R2AKT/eMMU/eMMU.kicad_sch

## KiCad design eMMU.kicad_sch (2026-06-29)

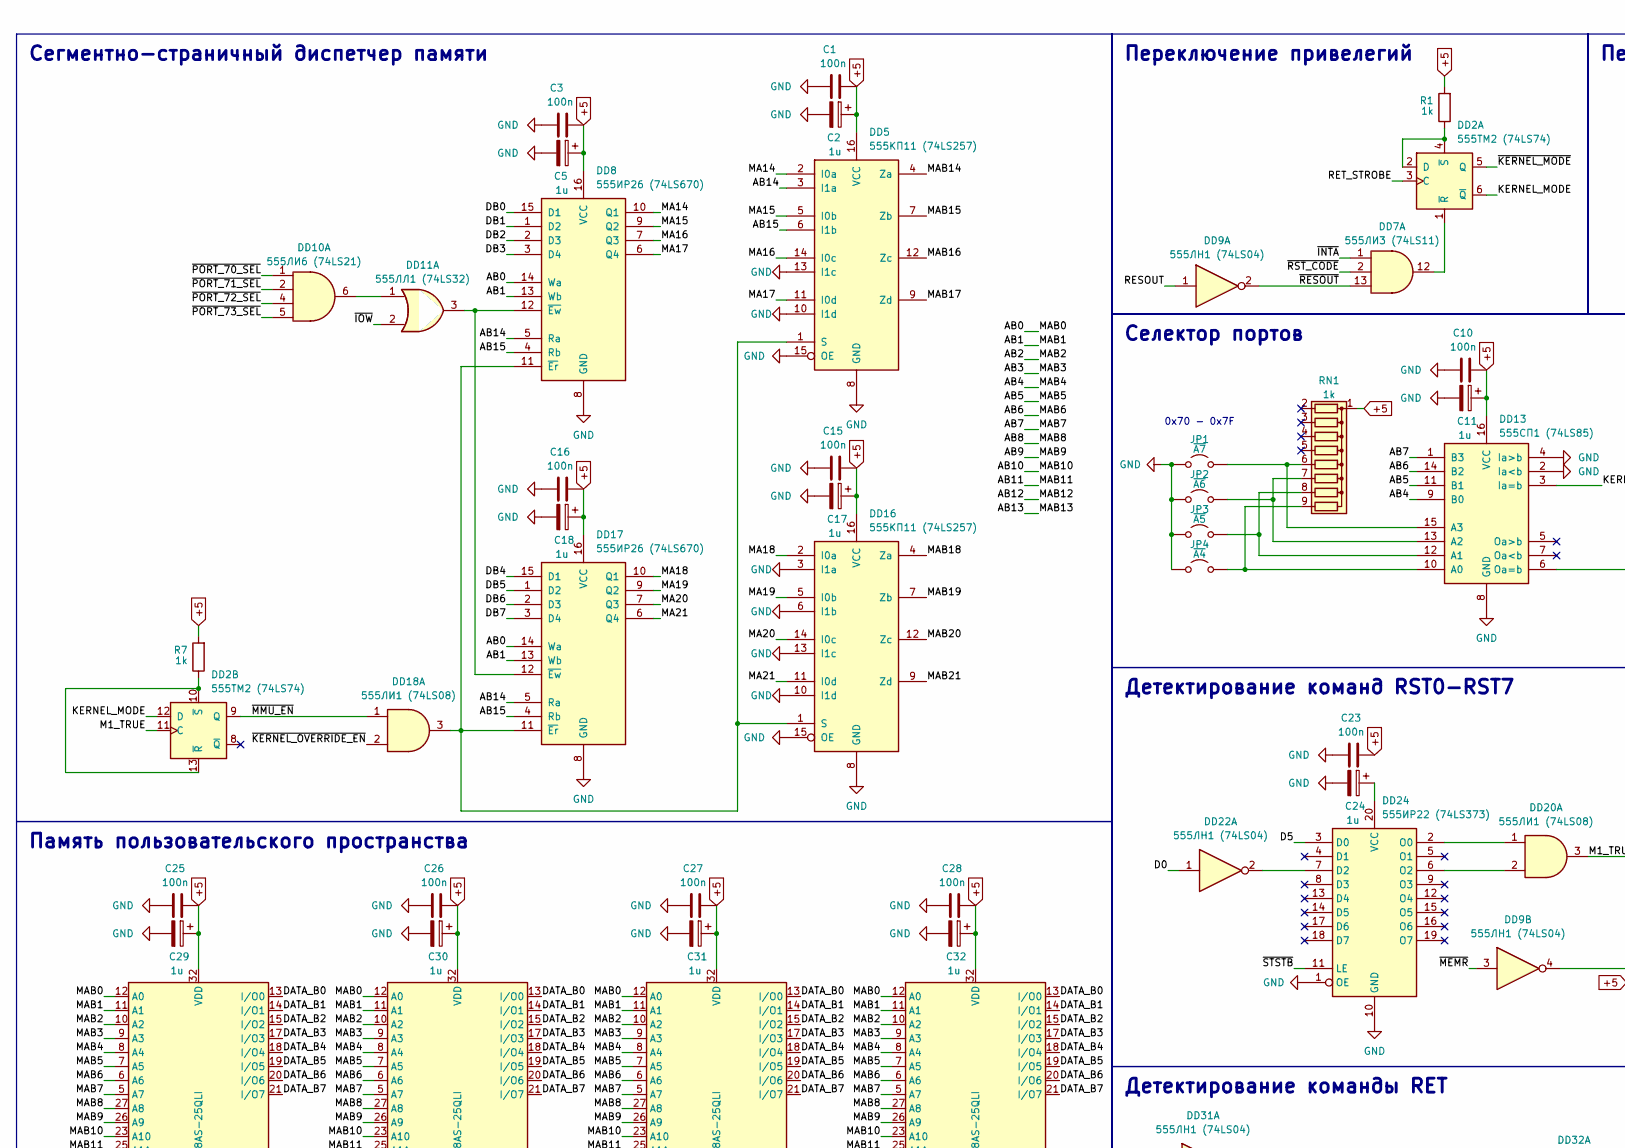
[picture p2: schematic eMMU.kicad_sch, part in row 1, column 1]

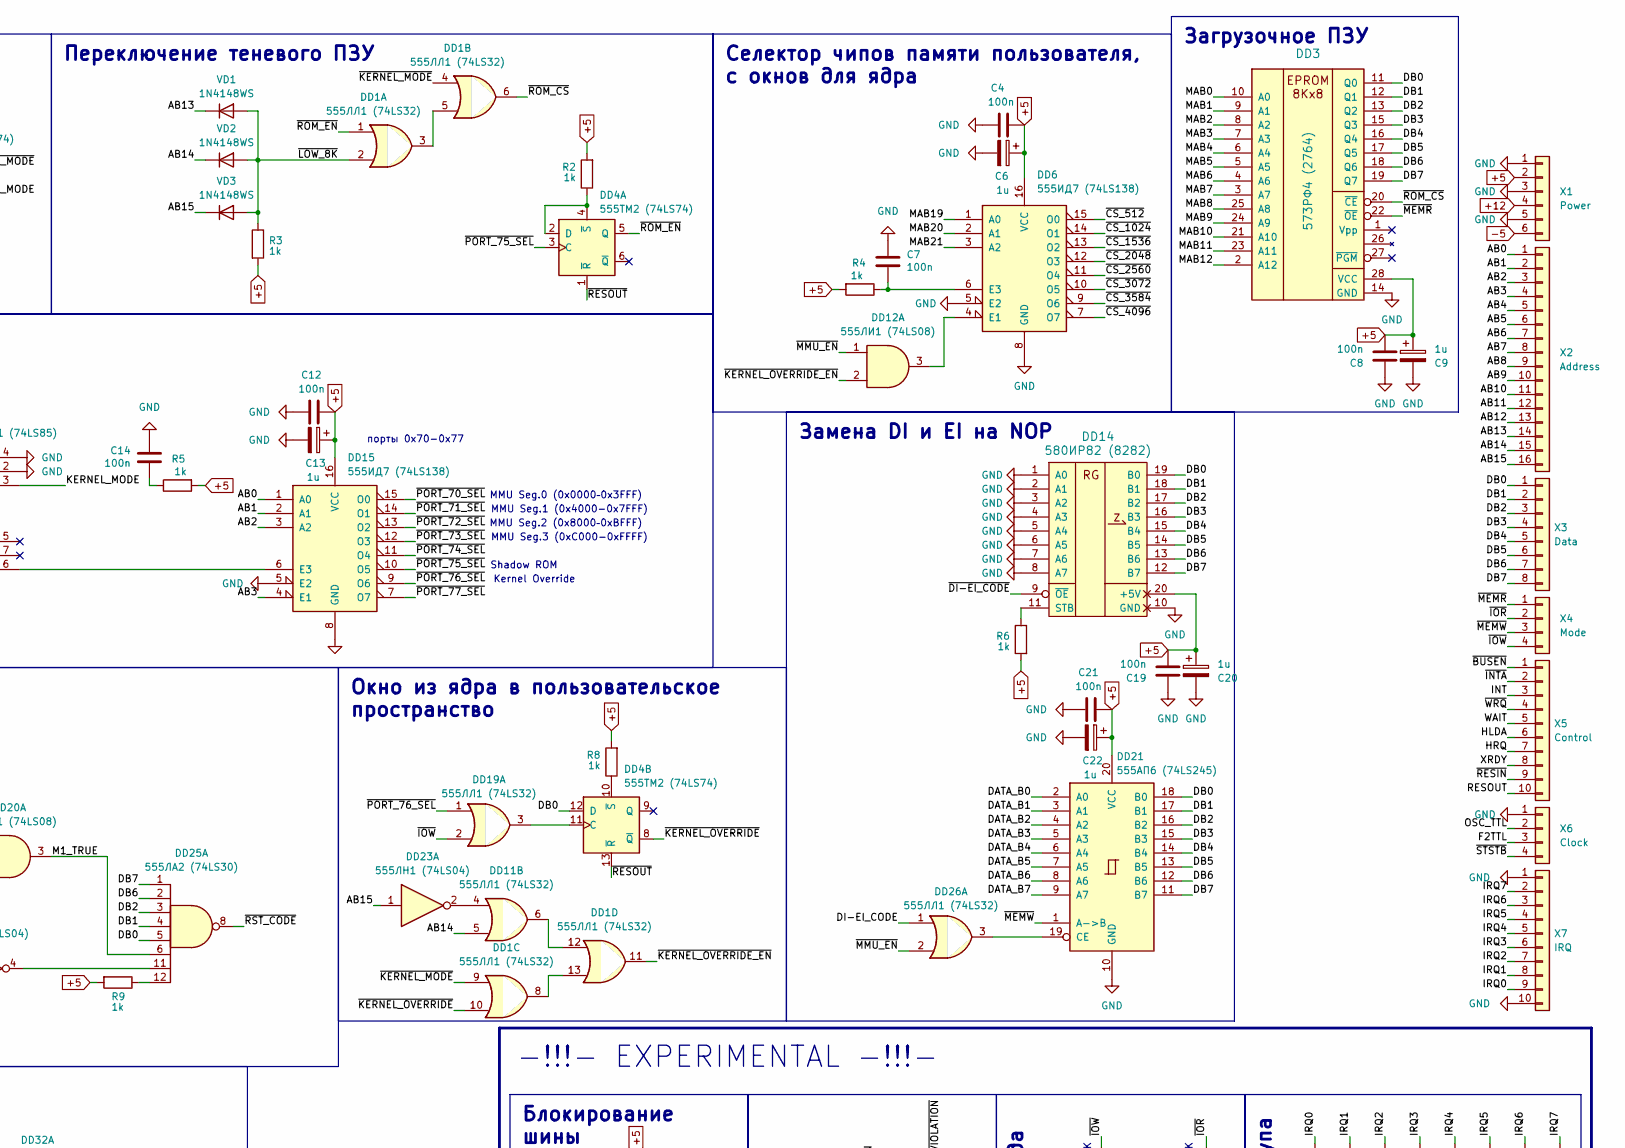
[picture p3: schematic eMMU.kicad_sch, part in row 1, column 2]

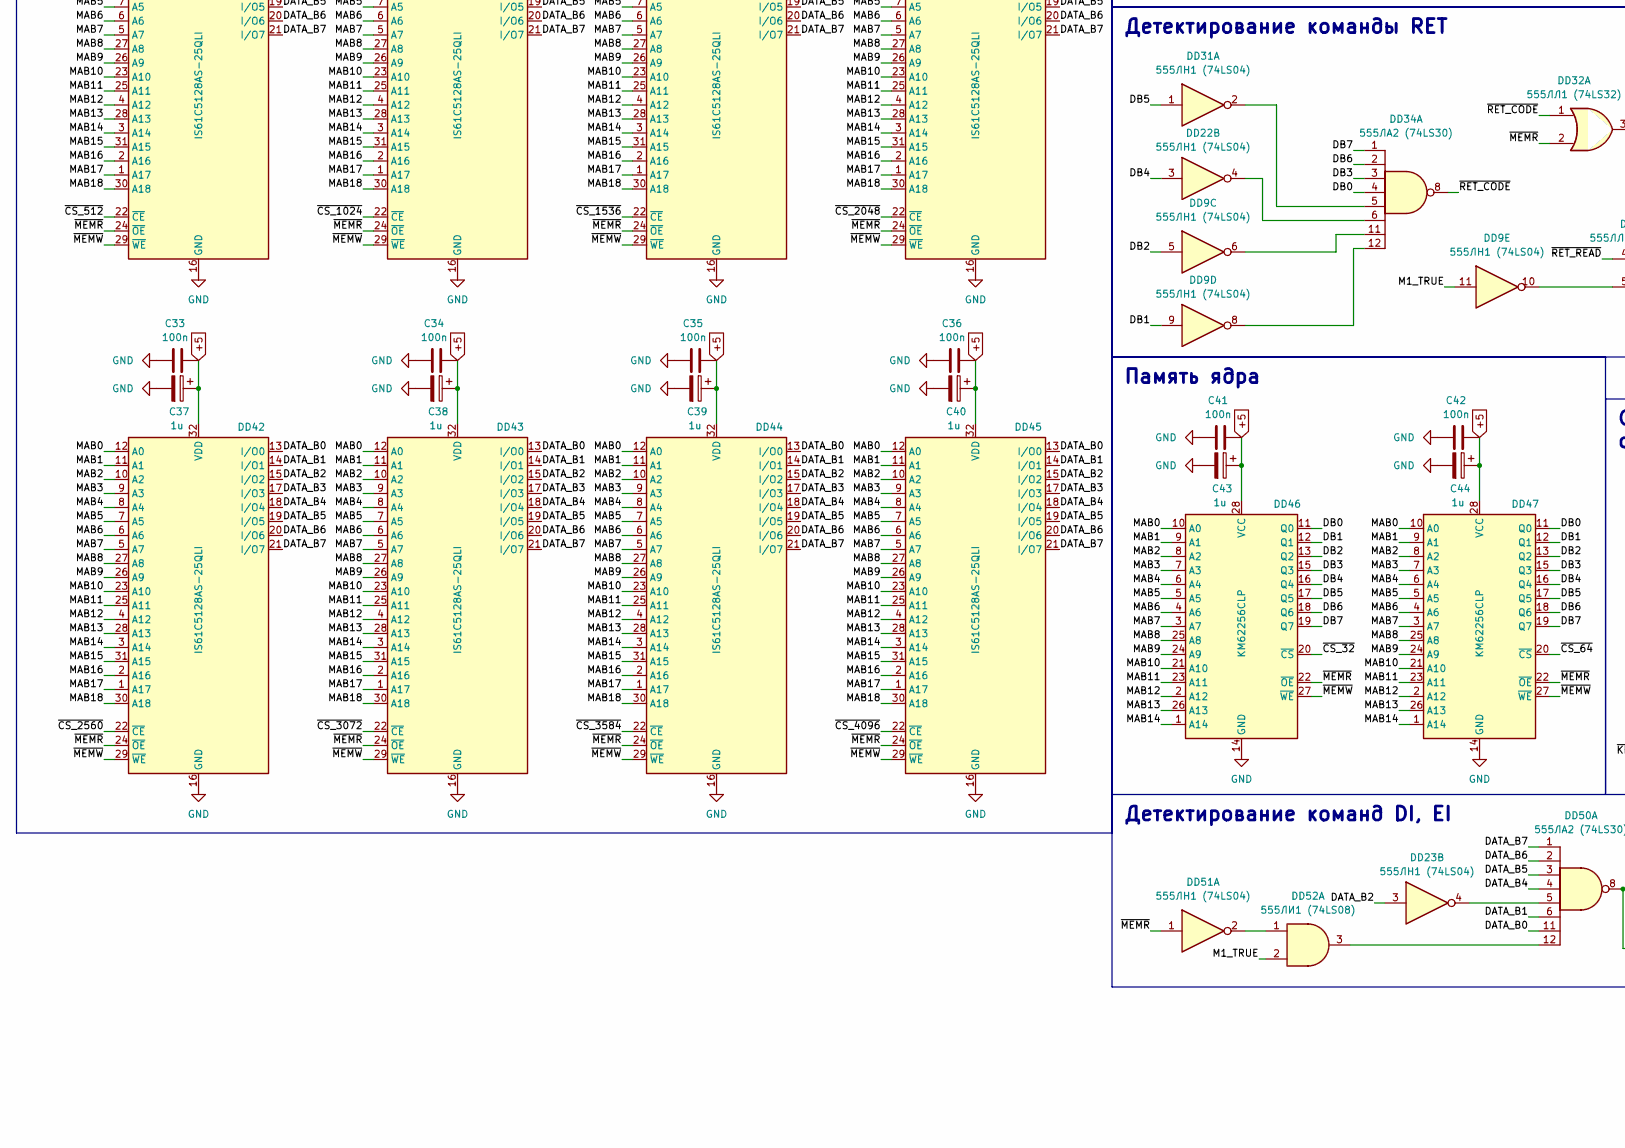
[picture p4: schematic eMMU.kicad_sch, part in row 2, column 1]

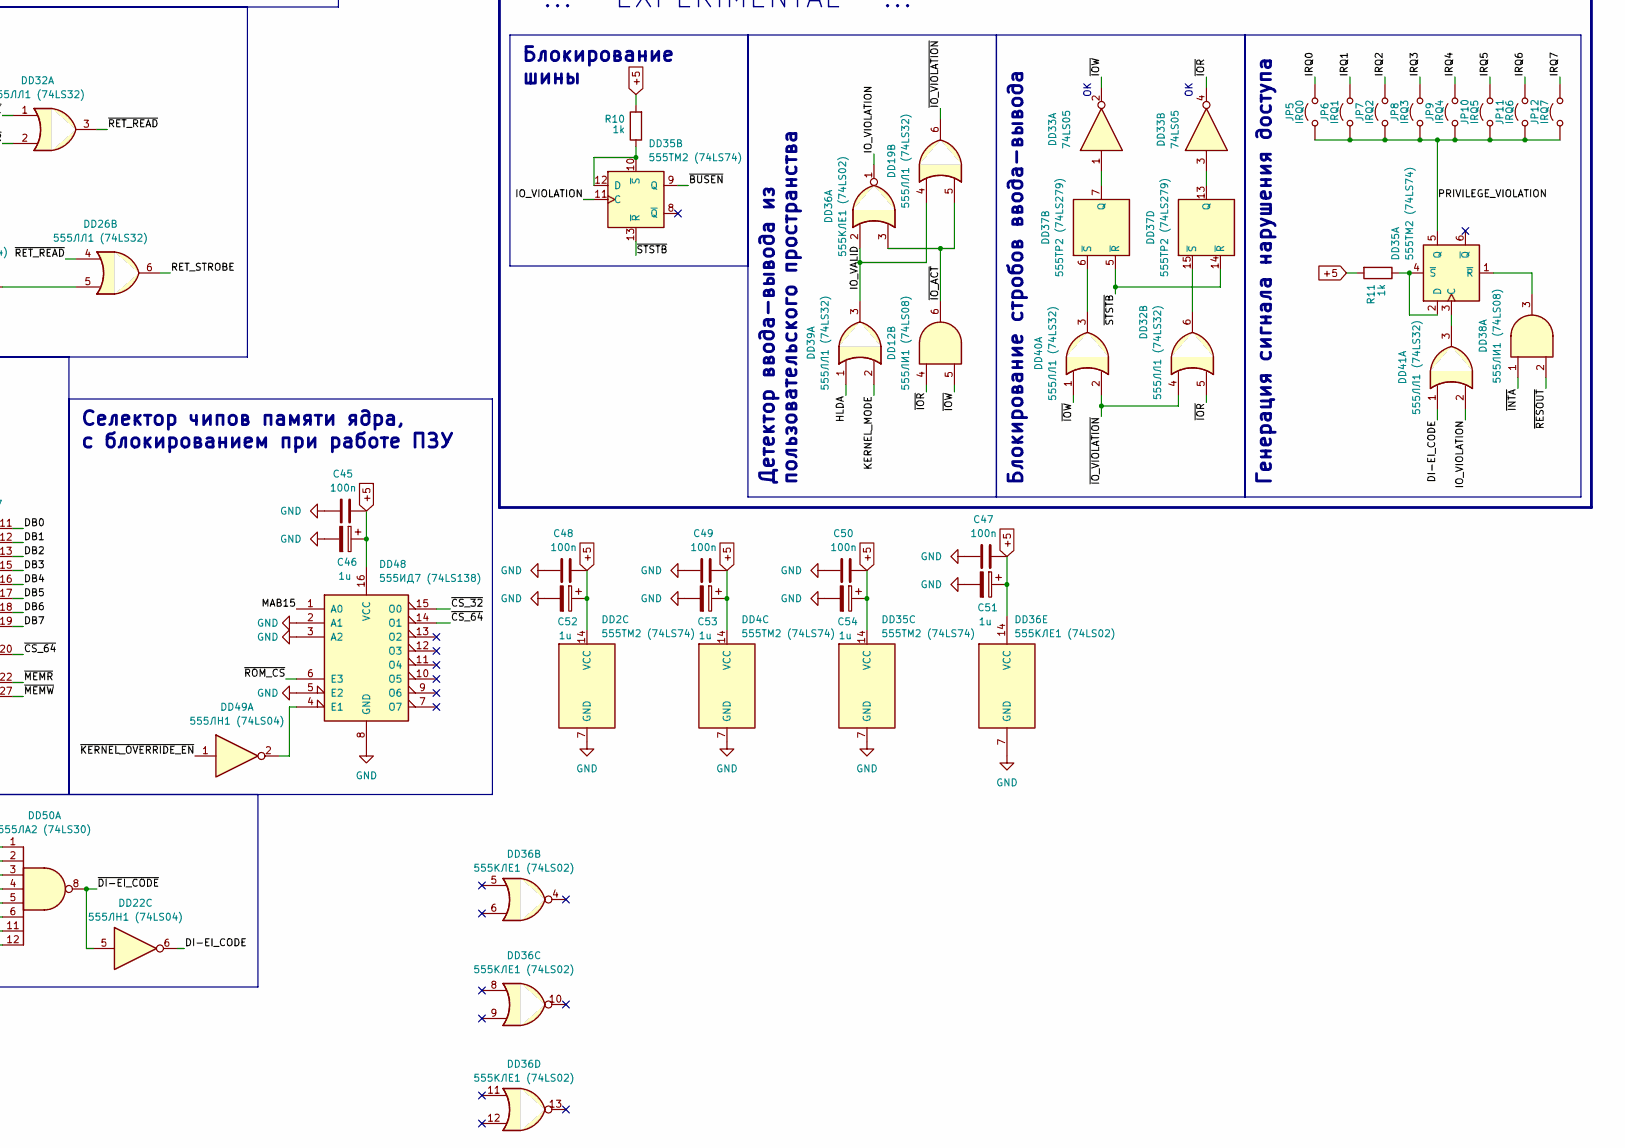
[picture p5: schematic eMMU.kicad_sch, part in row 2, column 2]

Parts:
C1, C3, C4, C7, C8, C10, C12, C14, C15, C16, C19, C21, C23, C25, C26, C27, C28, C33, C34, C35, C36, C41, C42, C45, C47, C48, C49, C50: 100n; C_0805_2012Metric_Pad1.18x1.45mm_HandSolder
C2, C5, C6, C9, C11, C13, C17, C18, C20, C22, C24, C29, C30, C31, C32, C37, C38, C39, C40, C43, C44, C46, C51, C52, C53, C54: 1u; CP_EIA-3216-18_Kemet-A_Pad1.58x1.35mm_HandSolder
DD1, DD11, DD19, DD26, DD32, DD39, DD40, DD41: 555ЛЛ1 (74LS32); SOIC-14_3.9x8.7mm_P1.27mm
DD2, DD4, DD35: 555ТМ2 (74LS74); SOIC-14_3.9x8.7mm_P1.27mm
DD3: 573РФ4 (2764); DIP-28_W15.24mm_Socket_LongPads
DD5, DD16: 555КП11 (74LS257); SOIC-16_4.55x10.3mm_P1.27mm
DD6, DD15, DD48: 555ИД7 (74LS138); SOIC-16_4.55x10.3mm_P1.27mm
DD7: 555ЛИ3 (74LS11); SOIC-14_3.9x8.7mm_P1.27mm
DD8, DD17: 555ИР26 (74LS670); SOIC-16_4.55x10.3mm_P1.27mm
DD9, DD22, DD23, DD31, DD49, DD51: 555ЛН1 (74LS04); SOIC-14_3.9x8.7mm_P1.27mm
DD10: 555ЛИ6 (74LS21); SOIC-14_3.9x8.7mm_P1.27mm
DD12, DD18, DD20, DD38, DD52: 555ЛИ1 (74LS08); SOIC-14_3.9x8.7mm_P1.27mm
DD13: 555СП1 (74LS85); SOIC-16_4.55x10.3mm_P1.27mm
DD14: 580ИР82 (8282); DIP-20_W7.62mm_LongPads
DD21: 555АП6 (74LS245); DIP-20_W7.62mm_Socket_LongPads
DD24: 555ИР22 (74LS373); SOIC-20W_7.5x12.8mm_P1.27mm
DD25, DD34, DD50: 555ЛА2 (74LS30); SOIC-14_3.9x8.7mm_P1.27mm
DD27, DD28, DD29, DD30, DD42, DD43, DD44, DD45: IS61C5128AS-25QLI; SOP-32_11.305x20.495mm_P1.27mm
DD33: 74LS05; SOIC-14_3.9x8.7mm_P1.27mm
DD36: 555KЛЕ1 (74LS02); SOIC-14_3.9x8.7mm_P1.27mm
DD37: 555ТР2 (74LS279); SOIC-16_4.55x10.3mm_P1.27mm
DD46, DD47: KM62256CLP; SOP-28_8.4x18.16mm_P1.27mm
JP1: ~{A7}; SolderJumper-2_P1.3mm_Open_RoundedPad1.0x1.5mm
JP2: ~{A6}; SolderJumper-2_P1.3mm_Open_RoundedPad1.0x1.5mm
JP3: ~{A5}; SolderJumper-2_P1.3mm_Open_RoundedPad1.0x1.5mm
JP4: ~{A4}; SolderJumper-2_P1.3mm_Open_RoundedPad1.0x1.5mm
JP5: IRQ0; SolderJumper-2_P1.3mm_Open_RoundedPad1.0x1.5mm
JP6: IRQ1; SolderJumper-2_P1.3mm_Open_RoundedPad1.0x1.5mm
JP7: IRQ2; SolderJumper-2_P1.3mm_Open_RoundedPad1.0x1.5mm
JP8: IRQ3; SolderJumper-2_P1.3mm_Open_RoundedPad1.0x1.5mm
JP9: IRQ4; SolderJumper-2_P1.3mm_Open_RoundedPad1.0x1.5mm
JP10: IRQ5; SolderJumper-2_P1.3mm_Open_RoundedPad1.0x1.5mm
JP11: IRQ6; SolderJumper-2_P1.3mm_Open_RoundedPad1.0x1.5mm
JP12: IRQ7; SolderJumper-2_P1.3mm_Open_RoundedPad1.0x1.5mm
R1, R2, R3, R4, R5, R6, R7, R8, R9, R10, R11: 1k; R_0805_2012Metric_Pad1.20x1.40mm_HandSolder
RN1: 1k; R_Array_SIP9
VD1, VD2, VD3: 1N4148WS; D_SOD-323_HandSoldering
X1: Power; PinHeader_1x06_P2.54mm_Vertical
X2: Address; PinHeader_1x16_P2.54mm_Vertical
X3: Data; PinHeader_1x08_P2.54mm_Vertical
X4: Mode; PinHeader_1x04_P2.54mm_Vertical
X5: Control; PinHeader_1x10_P2.54mm_Vertical
X6: Clock; PinHeader_1x04_P2.54mm_Vertical
X7: IRQ; PinHeader_1x10_P2.54mm_Vertical

Connections:
+5: C1.1, C2.1, C3.1, C4.1, C5.1, C6.1, C8.1, C9.1, C10.1, C11.1, C12.1, C13.1, C15.1, C16.1, C17.1, C18.1, C19.1, C20.1, C21.1, C22.1, C23.1, C25.1, C26.1, C27.1, C28.1, C29.1, C30.1, C31.1, C32.1, C33.1, C34.1, C35.1, C36.1, C37.1, C38.1, C39.1, C40.1, C41.1, C42.1, C43.1, C44.1, C45.1, C46.1, C47.1, C48.1, C49.1, C50.1, C51.1, C52.1, C53.1, C54.1, DD2.14 (VCC), DD3.28 (VCC), DD4.14 (VCC), DD5.16 (VCC), DD6.16 (VCC), DD8.16 (VCC), DD13.16 (VCC), DD14.20 (+5V), DD15.16 (VCC), DD16.16 (VCC), DD17.16 (VCC), DD21.20 (VCC), DD27.32 (VDD), DD28.32 (VDD), DD29.32 (VDD), DD30.32 (VDD), DD35.14 (VCC), DD36.14 (VCC), DD42.32 (VDD), DD43.32 (VDD), DD44.32 (VDD), DD45.32 (VDD), DD46.28 (VCC), DD47.28 (VCC), DD48.16 (VCC), R1.2, R2.2, R3.2, R4.2, R5.2, R6.2, R7.2, R8.2, R9.2, R10.2, R11.2, RN1.1 (common), X1.2
+12: X1.4
-5: X1.6
AB0: DD3.10 (A0), DD8.14 (Wa), DD15.1 (A0), DD17.14 (Wa), DD27.12 (A0), DD28.12 (A0), DD29.12 (A0), DD30.12 (A0), DD42.12 (A0), DD43.12 (A0), DD44.12 (A0), DD45.12 (A0), DD46.10 (A0), DD47.10 (A0), X2.1
AB1: DD3.9 (A1), DD8.13 (Wb), DD15.2 (A1), DD17.13 (Wb), DD27.11 (A1), DD28.11 (A1), DD29.11 (A1), DD30.11 (A1), DD42.11 (A1), DD43.11 (A1), DD44.11 (A1), DD45.11 (A1), DD46.9 (A1), DD47.9 (A1), X2.2
AB2: DD3.8 (A2), DD15.3 (A2), DD27.10 (A2), DD28.10 (A2), DD29.10 (A2), DD30.10 (A2), DD42.10 (A2), DD43.10 (A2), DD44.10 (A2), DD45.10 (A2), DD46.8 (A2), DD47.8 (A2), X2.3
AB3: DD3.7 (A3), DD15.4 (E1), DD27.9 (A3), DD28.9 (A3), DD29.9 (A3), DD30.9 (A3), DD42.9 (A3), DD43.9 (A3), DD44.9 (A3), DD45.9 (A3), DD46.7 (A3), DD47.7 (A3), X2.4
AB4: DD3.6 (A4), DD13.9 (B0), DD27.8 (A4), DD28.8 (A4), DD29.8 (A4), DD30.8 (A4), DD42.8 (A4), DD43.8 (A4), DD44.8 (A4), DD45.8 (A4), DD46.6 (A4), DD47.6 (A4), X2.5
AB5: DD3.5 (A5), DD13.11 (B1), DD27.7 (A5), DD28.7 (A5), DD29.7 (A5), DD30.7 (A5), DD42.7 (A5), DD43.7 (A5), DD44.7 (A5), DD45.7 (A5), DD46.5 (A5), DD47.5 (A5), X2.6
AB6: DD3.4 (A6), DD13.14 (B2), DD27.6 (A6), DD28.6 (A6), DD29.6 (A6), DD30.6 (A6), DD42.6 (A6), DD43.6 (A6), DD44.6 (A6), DD45.6 (A6), DD46.4 (A6), DD47.4 (A6), X2.7
AB7: DD3.3 (A7), DD13.1 (B3), DD27.5 (A7), DD28.5 (A7), DD29.5 (A7), DD30.5 (A7), DD42.5 (A7), DD43.5 (A7), DD44.5 (A7), DD45.5 (A7), DD46.3 (A7), DD47.3 (A7), X2.8
AB8: DD3.25 (A8), DD27.27 (A8), DD28.27 (A8), DD29.27 (A8), DD30.27 (A8), DD42.27 (A8), DD43.27 (A8), DD44.27 (A8), DD45.27 (A8), DD46.25 (A8), DD47.25 (A8), X2.9
AB9: DD3.24 (A9), DD27.26 (A9), DD28.26 (A9), DD29.26 (A9), DD30.26 (A9), DD42.26 (A9), DD43.26 (A9), DD44.26 (A9), DD45.26 (A9), DD46.24 (A9), DD47.24 (A9), X2.10
AB10: DD3.21 (A10), DD27.23 (A10), DD28.23 (A10), DD29.23 (A10), DD30.23 (A10), DD42.23 (A10), DD43.23 (A10), DD44.23 (A10), DD45.23 (A10), DD46.21 (A10), DD47.21 (A10), X2.11
AB11: DD3.23 (A11), DD27.25 (A11), DD28.25 (A11), DD29.25 (A11), DD30.25 (A11), DD42.25 (A11), DD43.25 (A11), DD44.25 (A11), DD45.25 (A11), DD46.23 (A11), DD47.23 (A11), X2.12
AB12: DD3.2 (A12), DD27.4 (A12), DD28.4 (A12), DD29.4 (A12), DD30.4 (A12), DD42.4 (A12), DD43.4 (A12), DD44.4 (A12), DD45.4 (A12), DD46.2 (A12), DD47.2 (A12), X2.13
AB13: DD27.28 (A13), DD28.28 (A13), DD29.28 (A13), DD30.28 (A13), DD42.28 (A13), DD43.28 (A13), DD44.28 (A13), DD45.28 (A13), DD46.26 (A13), DD47.26 (A13), VD1.1 (K), X2.14
AB14: DD5.3 (I1a), DD8.5 (Ra), DD11.5, DD17.5 (Ra), VD2.1 (K), X2.15
AB15: DD5.6 (I1b), DD8.4 (Rb), DD17.4 (Rb), DD23.1, VD3.1 (K), X2.16
D0: DD22.1
D5: DD24.3 (D0)
DATA_B0: DD21.2 (A0), DD27.13 (I/O0), DD28.13 (I/O0), DD29.13 (I/O0), DD30.13 (I/O0), DD42.13 (I/O0), DD43.13 (I/O0), DD44.13 (I/O0), DD45.13 (I/O0), DD50.11
DATA_B1: DD21.3 (A1), DD27.14 (I/O1), DD28.14 (I/O1), DD29.14 (I/O1), DD30.14 (I/O1), DD42.14 (I/O1), DD43.14 (I/O1), DD44.14 (I/O1), DD45.14 (I/O1), DD50.6
DATA_B2: DD21.4 (A2), DD23.3, DD27.15 (I/O2), DD28.15 (I/O2), DD29.15 (I/O2), DD30.15 (I/O2), DD42.15 (I/O2), DD43.15 (I/O2), DD44.15 (I/O2), DD45.15 (I/O2)
DATA_B3: DD21.5 (A3), DD27.17 (I/O3), DD28.17 (I/O3), DD29.17 (I/O3), DD30.17 (I/O3), DD42.17 (I/O3), DD43.17 (I/O3), DD44.17 (I/O3), DD45.17 (I/O3)
DATA_B4: DD21.6 (A4), DD27.18 (I/O4), DD28.18 (I/O4), DD29.18 (I/O4), DD30.18 (I/O4), DD42.18 (I/O4), DD43.18 (I/O4), DD44.18 (I/O4), DD45.18 (I/O4), DD50.4
DATA_B5: DD21.7 (A5), DD27.19 (I/O5), DD28.19 (I/O5), DD29.19 (I/O5), DD30.19 (I/O5), DD42.19 (I/O5), DD43.19 (I/O5), DD44.19 (I/O5), DD45.19 (I/O5), DD50.3
DATA_B6: DD21.8 (A6), DD27.20 (I/O6), DD28.20 (I/O6), DD29.20 (I/O6), DD30.20 (I/O6), DD42.20 (I/O6), DD43.20 (I/O6), DD44.20 (I/O6), DD45.20 (I/O6), DD50.2
DATA_B7: DD21.9 (A7), DD27.21 (I/O7), DD28.21 (I/O7), DD29.21 (I/O7), DD30.21 (I/O7), DD42.21 (I/O7), DD43.21 (I/O7), DD44.21 (I/O7), DD45.21 (I/O7), DD50.1
DB0: DD3.11 (Q0), DD4.12 (D), DD8.15 (D1), DD14.19 (B0), DD21.18 (B0), DD25.5, DD34.4, DD46.11 (Q0), DD47.11 (Q0), X3.1
DB1: DD3.12 (Q1), DD8.1 (D2), DD9.9, DD14.18 (B1), DD21.17 (B1), DD25.4, DD46.12 (Q1), DD47.12 (Q1), X3.2
DB2: DD3.13 (Q2), DD8.2 (D3), DD9.5, DD14.17 (B2), DD21.16 (B2), DD25.3, DD46.13 (Q2), DD47.13 (Q2), X3.3
DB3: DD3.15 (Q3), DD8.3 (D4), DD14.16 (B3), DD21.15 (B3), DD34.3, DD46.15 (Q3), DD47.15 (Q3), X3.4
DB4: DD3.16 (Q4), DD14.15 (B4), DD17.15 (D1), DD21.14 (B4), DD22.3, DD46.16 (Q4), DD47.16 (Q4), X3.5
DB5: DD3.17 (Q5), DD14.14 (B5), DD17.1 (D2), DD21.13 (B5), DD31.1, DD46.17 (Q5), DD47.17 (Q5), X3.6
DB6: DD3.18 (Q6), DD14.13 (B6), DD17.2 (D3), DD21.12 (B6), DD25.2, DD34.2, DD46.18 (Q6), DD47.18 (Q6), X3.7
DB7: DD3.19 (Q7), DD14.12 (B7), DD17.3 (D4), DD21.11 (B7), DD25.1, DD34.1, DD46.19 (Q7), DD47.19 (Q7), X3.8
DI-EI_CODE: DD22.6, DD26.1, DD41.1
F2TTL: X6.3
GND: C1.2, C2.2, C3.2, C4.2, C5.2, C6.2, C7.1, C8.2, C9.2, C10.2, C11.2, C12.2, C13.2, C14.1, C15.2, C16.2, C17.2, C18.2, C19.2, C20.2, C21.2, C22.2, C23.2, C24.2, C25.2, C26.2, C27.2, C28.2, C29.2, C30.2, C31.2, C32.2, C33.2, C34.2, C35.2, C36.2, C37.2, C38.2, C39.2, C40.2, C41.2, C42.2, C43.2, C44.2, C45.2, C46.2, C47.2, C48.2, C49.2, C50.2, C51.2, C52.2, C53.2, C54.2, DD2.7 (GND), DD3.14 (GND), DD4.7 (GND), DD5.8 (GND), DD5.10 (I1d), DD5.13 (I1c), DD5.15 (OE), DD6.5 (E2), DD6.8 (GND), DD8.8 (GND), DD13.2 (Ia<b), DD13.4 (Ia>b), DD13.8 (GND), DD14.1 (A0), DD14.2 (A1), DD14.3 (A2), DD14.4 (A3), DD14.5 (A4), DD14.6 (A5), DD14.7 (A6), DD14.8 (A7), DD14.10 (GND), DD15.5 (E2), DD15.8 (GND), DD16.3 (I1a), DD16.6 (I1b), DD16.8 (GND), DD16.10 (I1d), DD16.13 (I1c), DD16.15 (OE), DD17.8 (GND), DD21.10 (GND), DD24.1 (OE), DD24.10 (GND), DD27.16 (GND), DD28.16 (GND), DD29.16 (GND), DD30.16 (GND), DD35.7 (GND), DD36.7 (GND), DD42.16 (GND), DD43.16 (GND), DD44.16 (GND), DD45.16 (GND), DD46.14 (GND), DD47.14 (GND), DD48.2 (A1), DD48.3 (A2), DD48.5 (E2), DD48.8 (GND), JP1.1 (A), JP2.1 (A), JP3.1 (A), JP4.1 (A), X1.1, X1.3, X1.5, X6.1, X7.1, X7.10
HLDA: DD39.1, X5.6
HRQ: X5.7
INT: X5.3
IO_VALID: DD19.4, DD36.2, DD39.3
IO_VIOLATION: DD35.11 (C), DD36.1, DD41.2
IRQ0: JP5.2 (B), X7.9
IRQ1: JP6.2 (B), X7.8
IRQ2: JP7.2 (B), X7.7
IRQ3: JP8.2 (B), X7.6
IRQ4: JP9.2 (B), X7.5
IRQ5: JP10.2 (B), X7.4
IRQ6: JP11.2 (B), X7.3
IRQ7: JP12.2 (B), X7.2
KERNEL_MODE: DD2.6 (~Q), DD2.12 (D), DD13.3 (Ia=b), DD39.2
M1_TRUE: DD2.11 (C), DD9.11, DD20.3, DD25.6, DD52.2
MA14: DD5.2 (I0a), DD8.10 (Q1)
MA15: DD5.5 (I0b), DD8.9 (Q2)
MA16: DD5.14 (I0c), DD8.7 (Q3)
MA17: DD5.11 (I0d), DD8.6 (Q4)
MA18: DD16.2 (I0a), DD17.10 (Q1)
MA19: DD16.5 (I0b), DD17.9 (Q2)
MA20: DD16.14 (I0c), DD17.7 (Q3)
MA21: DD16.11 (I0d), DD17.6 (Q4)
MAB14: DD5.4 (Za), DD27.3 (A14), DD28.3 (A14), DD29.3 (A14), DD30.3 (A14), DD42.3 (A14), DD43.3 (A14), DD44.3 (A14), DD45.3 (A14), DD46.1 (A14), DD47.1 (A14)
MAB15: DD5.7 (Zb), DD27.31 (A15), DD28.31 (A15), DD29.31 (A15), DD30.31 (A15), DD42.31 (A15), DD43.31 (A15), DD44.31 (A15), DD45.31 (A15), DD48.1 (A0)
MAB16: DD5.12 (Zc), DD27.2 (A16), DD28.2 (A16), DD29.2 (A16), DD30.2 (A16), DD42.2 (A16), DD43.2 (A16), DD44.2 (A16), DD45.2 (A16)
MAB17: DD5.9 (Zd), DD27.1 (A17), DD28.1 (A17), DD29.1 (A17), DD30.1 (A17), DD42.1 (A17), DD43.1 (A17), DD44.1 (A17), DD45.1 (A17)
MAB18: DD16.4 (Za), DD27.30 (A18), DD28.30 (A18), DD29.30 (A18), DD30.30 (A18), DD42.30 (A18), DD43.30 (A18), DD44.30 (A18), DD45.30 (A18)
MAB19: DD6.1 (A0), DD16.7 (Zb)
MAB20: DD6.2 (A1), DD16.12 (Zc)
MAB21: DD6.3 (A2), DD16.9 (Zd)
unnamed: C7.2, DD6.6 (E3), R4.1
unnamed: C14.2, R5.1
unnamed: C24.1, DD24.20 (VCC)
unnamed: DD1.3, DD1.5
unnamed: DD1.12, DD11.6
unnamed: DD1.8, DD1.13
unnamed: DD2.1 (~R), DD7.12
unnamed: DD2.2 (D), DD2.4 (~S), R1.1
unnamed: DD2.10 (~S), DD2.13 (~R), R7.1
unnamed: DD4.2 (D), DD4.4 (~S), R2.1
unnamed: DD4.10 (~S), R8.1
unnamed: DD10.6, DD11.1
unnamed: DD8.12 (~Ew), DD11.3, DD17.12 (~Ew)
unnamed: DD11.4, DD23.2
unnamed: DD6.4 (E1), DD12.3
unnamed: DD13.6 (Oa=b), DD15.6 (E3)
unnamed: DD13.10 (A0), JP4.2 (B), RN1.9 (R8)
unnamed: DD13.12 (A1), JP3.2 (B), RN1.8 (R7)
unnamed: DD13.13 (A2), JP2.2 (B), RN1.7 (R6)
unnamed: DD13.15 (A3), JP1.2 (B), RN1.6 (R5)
unnamed: DD14.11 (STB), R6.1
unnamed: DD5.1 (S), DD8.11 (~Er), DD16.1 (S), DD17.11 (~Er), DD18.3
unnamed: DD4.11 (C), DD19.3
unnamed: DD20.1, DD24.2 (O0)
unnamed: DD20.2, DD24.6 (O2)
unnamed: DD21.19 (CE), DD26.3
unnamed: DD22.2, DD24.7 (D2)
unnamed: DD22.4, DD34.6
unnamed: DD23.4, DD50.5
unnamed: DD9.4, DD25.11
unnamed: DD25.12, R9.1
unnamed: DD9.10, DD26.5
unnamed: DD31.2, DD34.5
unnamed: DD32.6, DD37.15 (~S)
unnamed: DD33.1, DD37.7 (Q)
unnamed: DD33.3, DD37.13 (Q)
unnamed: DD9.6, DD34.11
unnamed: DD9.8, DD34.12
unnamed: DD35.1 (~R), DD38.3
unnamed: DD35.2 (D), DD35.4 (~S), R11.1
unnamed: DD35.3 (C), DD41.3
unnamed: DD35.10 (~S), DD35.12 (D), R10.1
unnamed: DD37.6 (~S), DD40.3
unnamed: DD48.4 (E1), DD49.2
unnamed: DD50.12, DD52.3
unnamed: DD51.2, DD52.1
OSC_TTL: X6.2
PRIVILEGE_VIOLATION: DD35.5 (Q), JP5.1 (A), JP6.1 (A), JP7.1 (A), JP8.1 (A), JP9.1 (A), JP10.1 (A), JP11.1 (A), JP12.1 (A)
RESOUT: DD9.1, X5.10
RET_STROBE: DD2.3 (C), DD26.6
WAIT: X5.5
XRDY: X5.8
~BUSEN: DD35.9 (Q), X5.1
~CS_32: DD46.20 (~CS), DD48.15 (O0)
~CS_64: DD47.20 (~CS), DD48.14 (O1)
~CS_512: DD6.15 (O0), DD27.22 (~CE)
~CS_1024: DD6.14 (O1), DD28.22 (~CE)
~CS_1536: DD6.13 (O2), DD29.22 (~CE)
~CS_2048: DD6.12 (O3), DD30.22 (~CE)
~CS_2560: DD6.11 (O4), DD42.22 (~CE)
~CS_3072: DD6.10 (O5), DD43.22 (~CE)
~CS_3584: DD6.9 (O6), DD44.22 (~CE)
~CS_4096: DD6.7 (O7), DD45.22 (~CE)
~DI-EI_CODE: DD14.9 (~OE), DD22.5, DD50.8
~INTA: DD7.1, DD38.1, X5.2
~IOR: DD12.4, DD32.5, DD33.4, X4.2
~IOW: DD11.2, DD12.5, DD19.2, DD33.2, DD40.1, X4.4
~IO_ACT: DD12.6, DD19.5, DD36.3
~IO_VIOLATION: DD19.6, DD32.4, DD40.2
~KERNEL_MODE: DD1.4, DD1.9, DD2.5 (Q)
~KERNEL_OVERRIDE_EN: DD1.11, DD12.2, DD18.2, DD49.1
~KERNEL_OVERRIDE: DD1.10, DD4.8 (~Q)
~LOW_8K: DD1.2, R3.1, VD1.2 (A), VD2.2 (A), VD3.2 (A)
~MEMR: DD3.22 (~OE), DD9.3, DD27.24 (~OE), DD28.24 (~OE), DD29.24 (~OE), DD30.24 (~OE), DD32.2, DD42.24 (~OE), DD43.24 (~OE), DD44.24 (~OE), DD45.24 (~OE), DD46.22 (~OE), DD47.22 (~OE), DD51.1, X4.1
~MEMW: DD21.1 (A->B), DD27.29 (~WE), DD28.29 (~WE), DD29.29 (~WE), DD30.29 (~WE), DD42.29 (~WE), DD43.29 (~WE), DD44.29 (~WE), DD45.29 (~WE), DD46.27 (~WE), DD47.27 (~WE), X4.3
~MMU_EN: DD2.9 (Q), DD12.1, DD18.1, DD26.2
~PORT_70_SEL: DD10.1, DD15.15 (O0)
~PORT_71_SEL: DD10.2, DD15.14 (O1)
~PORT_72_SEL: DD10.4, DD15.13 (O2)
~PORT_73_SEL: DD10.5, DD15.12 (O3)
~PORT_74_SEL: DD15.11 (O4)
~PORT_75_SEL: DD4.3 (C), DD15.10 (O5)
~PORT_76_SEL: DD15.9 (O6), DD19.1
~PORT_77_SEL: DD15.7 (O7)
~RESIN: X5.9
~RESOUT: DD4.1 (~R), DD4.13 (~R), DD7.13, DD9.2, DD38.2
~RET_CODE: DD32.1, DD34.8
~RET_READ: DD26.4, DD32.3
~ROM_CS: DD1.6, DD3.20 (~CE), DD48.6 (E3)
~ROM_EN: DD1.1, DD4.5 (Q)
~RST_CODE: DD7.2, DD25.8
~STSTB: DD24.11 (LE), DD35.13 (~R), DD37.5 (~R), DD37.14 (~R), X6.4
~WRQ: X5.4

Notes on the sheet:
Детектор ввода-вывода из пользовательского пространства
Память пользовательского пространства
Селектор чипов памяти пользователя, с окнов для ядра
Генерация сигнала нарушения доступа
Блокирование шины
Переключение теневого ПЗУ
Окно из ядра в пользовательское пространство
Детектирование команды RET
Детектирование команд RST0-RST7
Память ядра
Сегментно-страничный диспетчер памяти
Переключение привелегий
-!!!- EXPERIMENTAL -!!!-
Селектор чипов памяти ядра, с блокированием при работе ПЗУ
Загрузочное ПЗУ
Детектирование команд DI, EI
Селектор портов
Блокирование стробов ввода-вывода
Замена DI и EI на NOP
Shadow ROM
MMU Seg.3 (0xC000-0xFFFF)
MMU Seg.0 (0x0000–0x3FFF)
порты 0x70-0x77
MMU Seg.1 (0x4000-0x7FFF)
0x70 - 0x7F
Kernel Override
MMU Seg.2 (0x8000–0xBFFF)
